PaulSchulz/paeiot-sensor-one/fritzing/board-v1_0.png

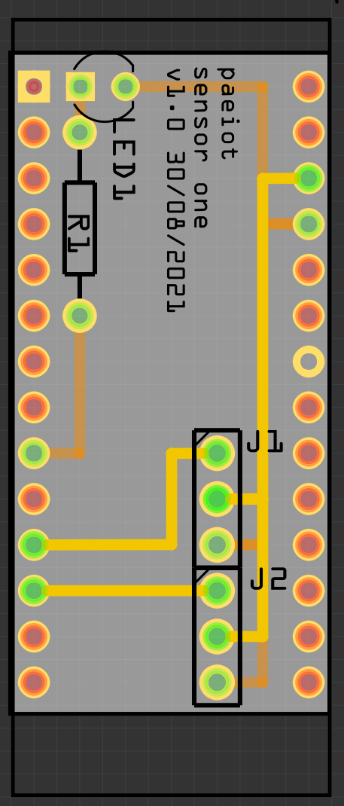
fritzing/board-v1_0.png
