PaulSchulz/paeiot-sensor-one/images/20210803_163039.jpg

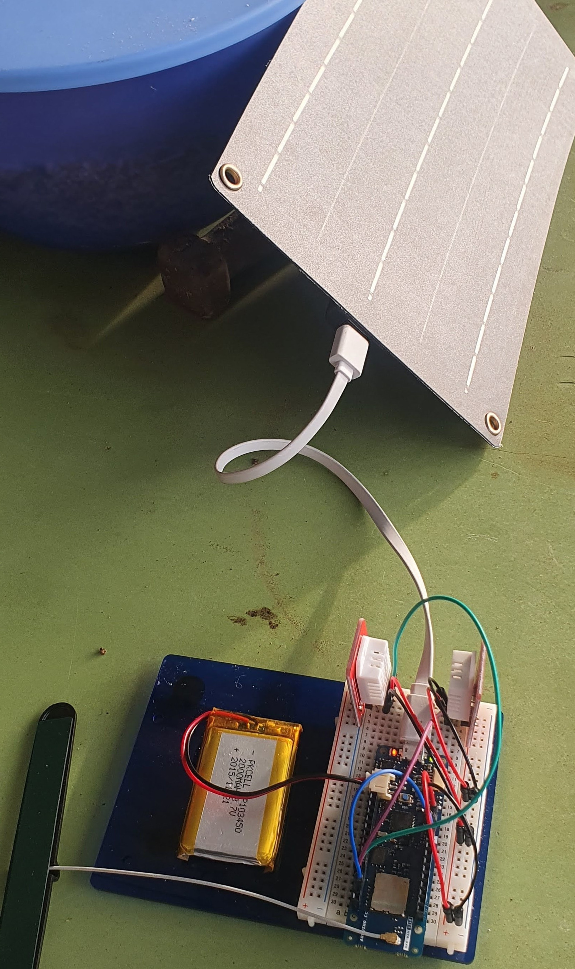
images/20210803_163039.jpg
