PaulSchulz/paeiot-sensor-one/images/20210814_2000_01.jpg

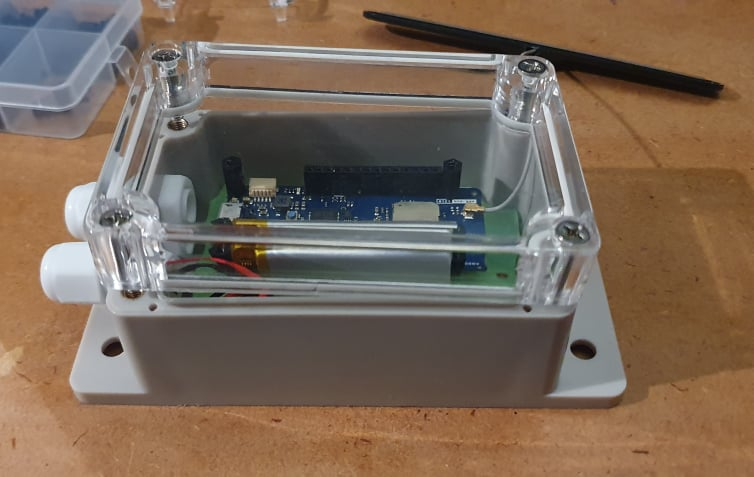
images/20210814_2000_01.jpg
