PaulSchulz/paeiot-sensor-one/images/20210823_110651_resized.jpg

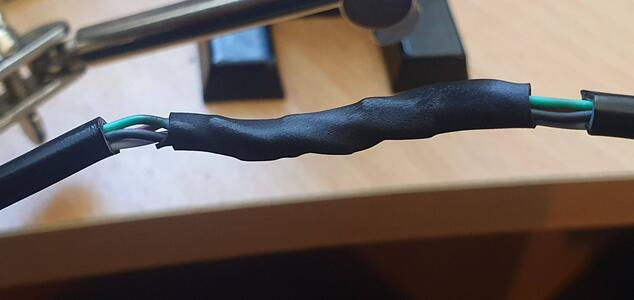
images/20210823_110651_resized.jpg
