PaulSchulz/paeiot-sensor-one/images/20210828_195500.jpg

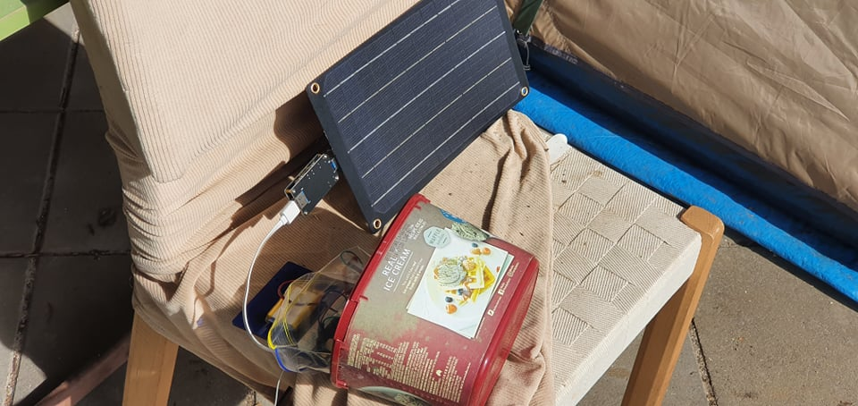
images/20210828_195500.jpg
