PaulSchulz/paeiot-sensor-one/images/20211008_182954.jpg

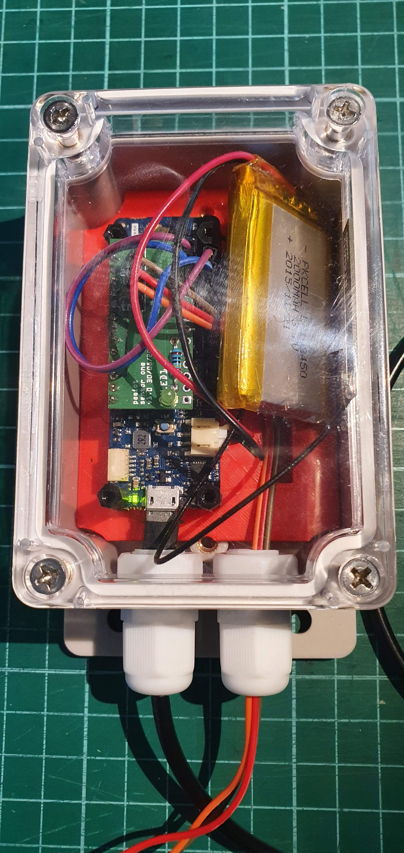
images/20211008_182954.jpg
