PaulSchulz/paeiot-sensor-one/images/20211029-093234.jpg

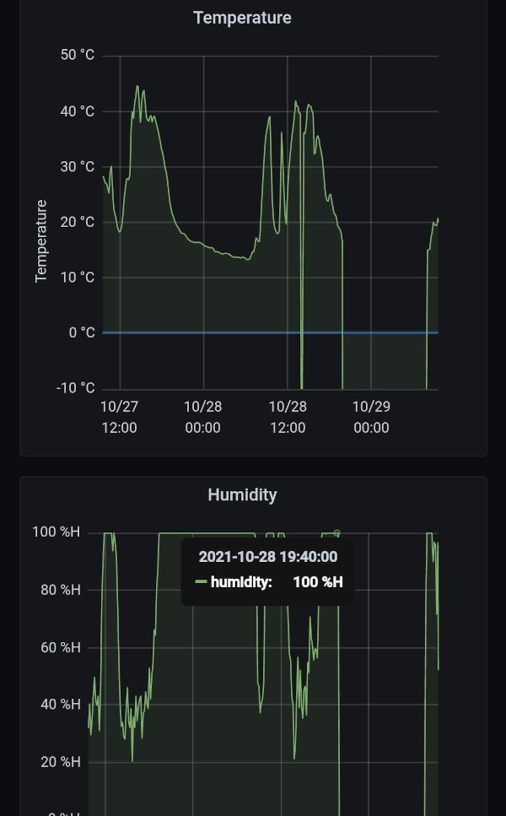
images/20211029-093234.jpg
