PaulSchulz/paeiot-sensor-one/images/228427619_3322535084639710_1404951063178568112_n.jpg

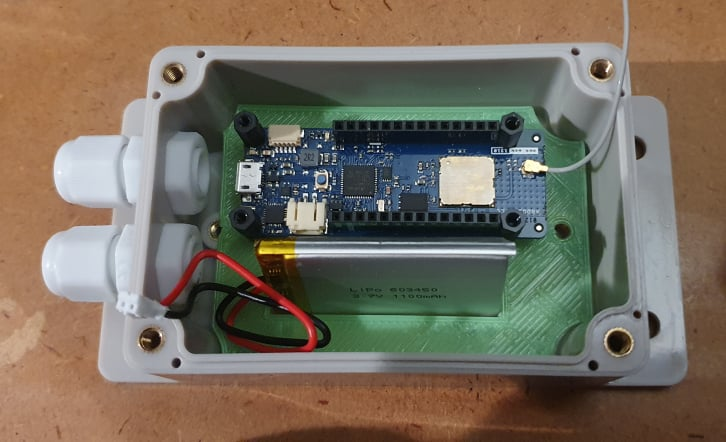
images/228427619_3322535084639710_1404951063178568112_n.jpg
