PaulSchulz/paeiot-sensor-one/images/230631305_171352048309334_1570531494024995739_n.jpg

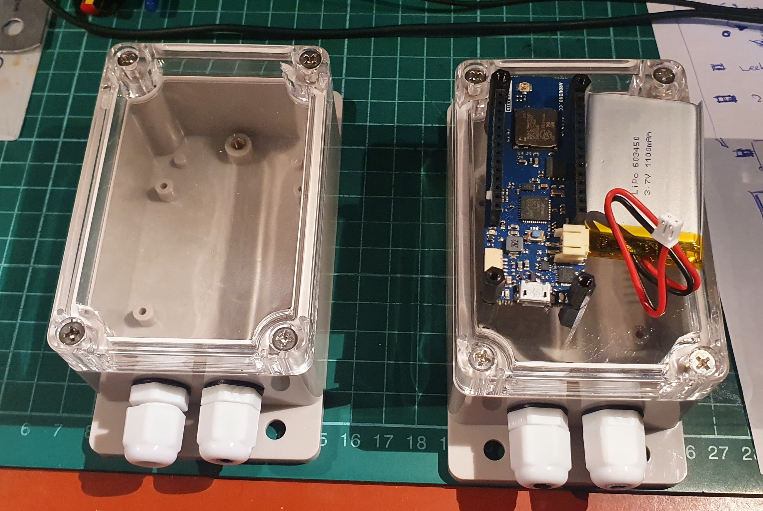
images/230631305_171352048309334_1570531494024995739_n.jpg
