PaulSchulz/paeiot-sensor-one/images/232836324_121206800151648_2778572270893868000_n.jpg

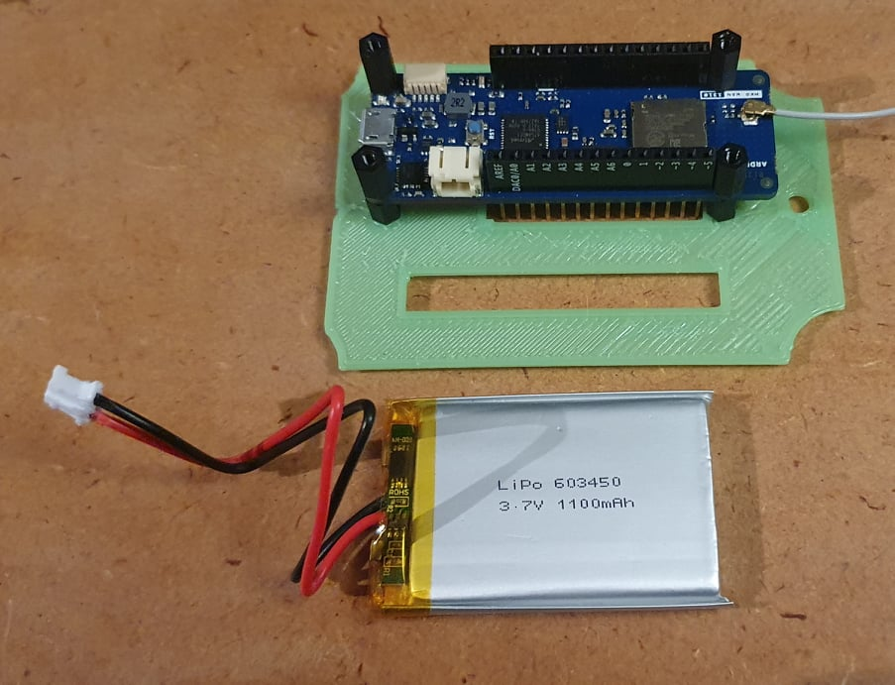
images/232836324_121206800151648_2778572270893868000_n.jpg
