PaulSchulz/paeiot-sensor-one/images/234786361_391616262325914_8475649943830079304_n.jpg

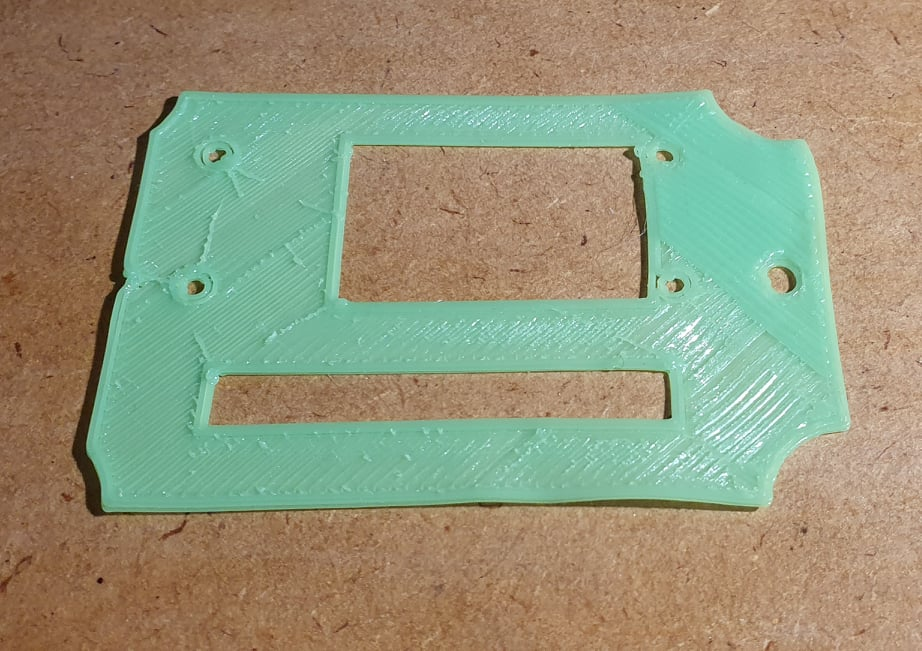
images/234786361_391616262325914_8475649943830079304_n.jpg
