PaulSchulz/paeiot-sensor-one/images/235867642_2991339191183786_8881488392173606955_n.jpg

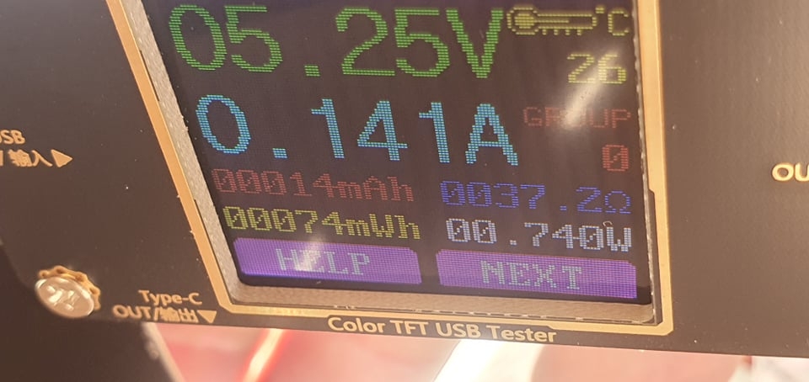
images/235867642_2991339191183786_8881488392173606955_n.jpg
