PaulSchulz/paeiot-sensor-one/images/MKRWAN1310-01.jpg

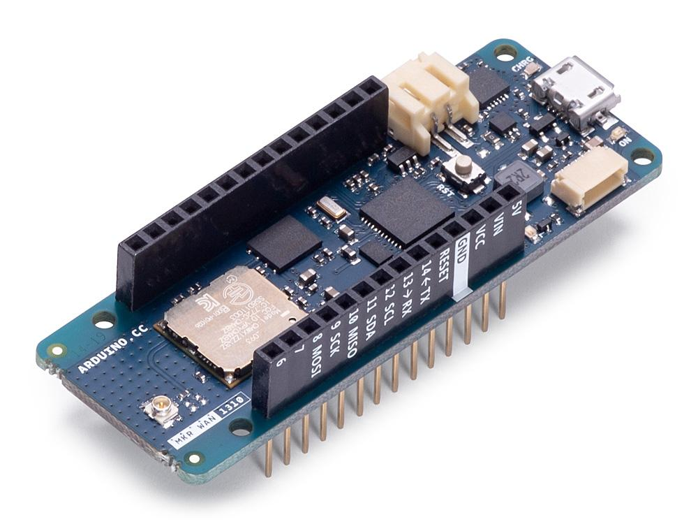
images/MKRWAN1310-01.jpg
