PaulSchulz/paeiot-sensor-one/images/MKRWAN1310-02.jpg

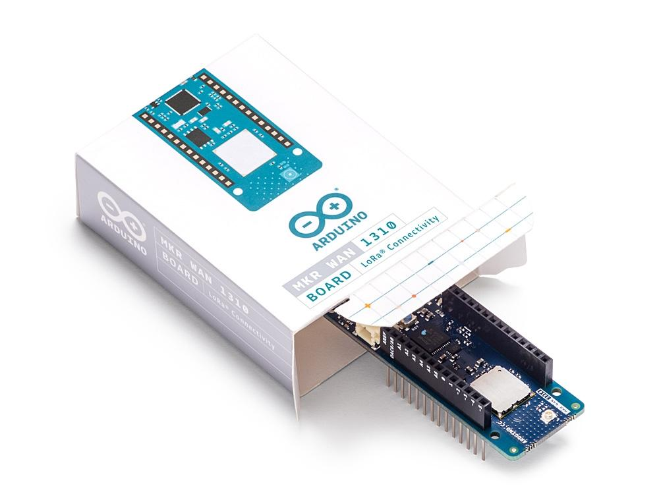
images/MKRWAN1310-02.jpg
