PaulSchulz/paeiot-sensor-one/images/MKRWAN1310-04.jpg

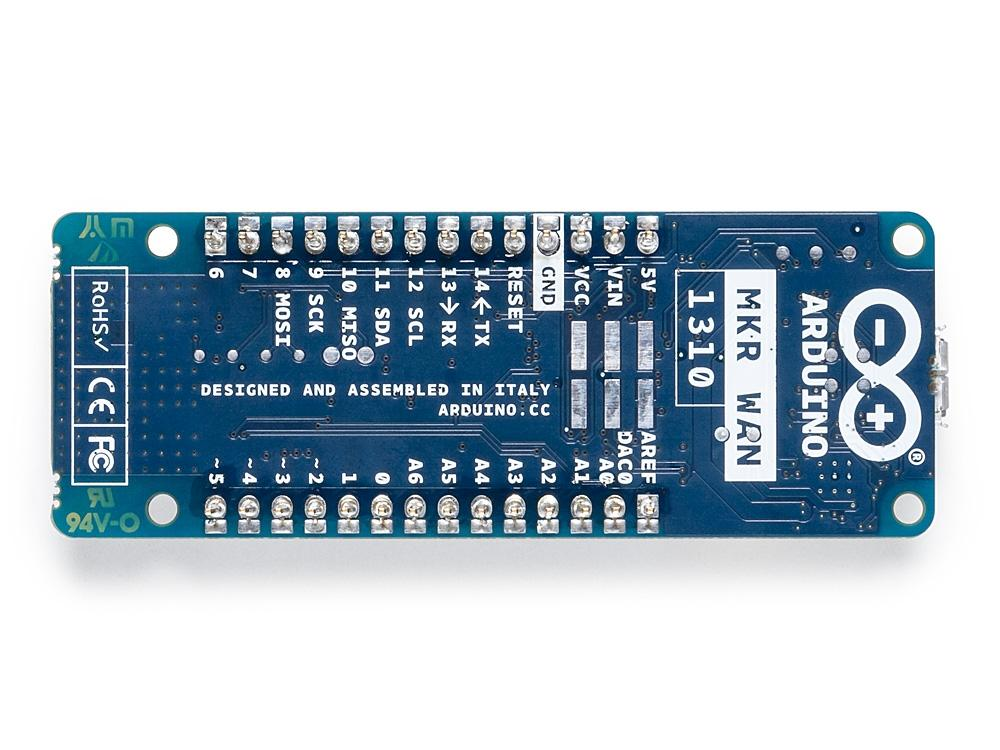
images/MKRWAN1310-04.jpg
