PaulSchulz/paeiot-sensor-one/images/MKRWAN1310-05.jpg

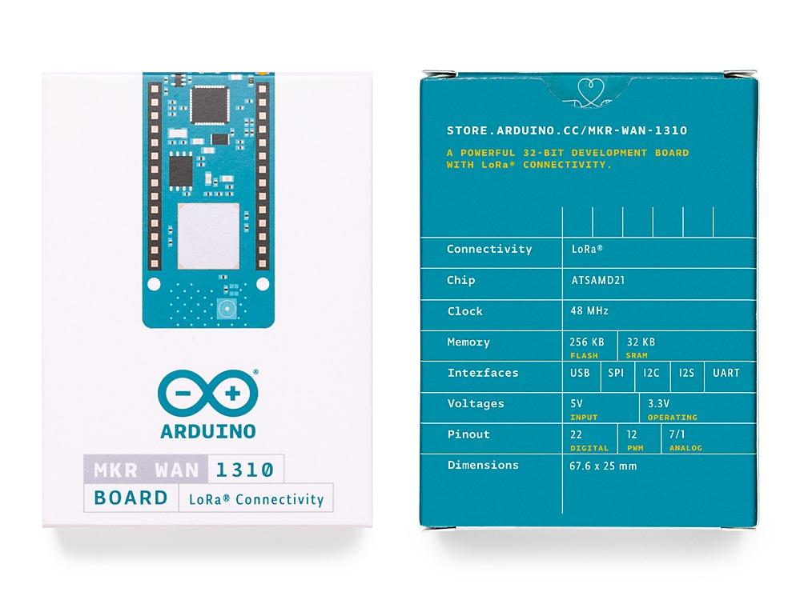
images/MKRWAN1310-05.jpg
