PaulSchulz/paeiot-sensor-one/images/MKRWAN1310-06.jpg

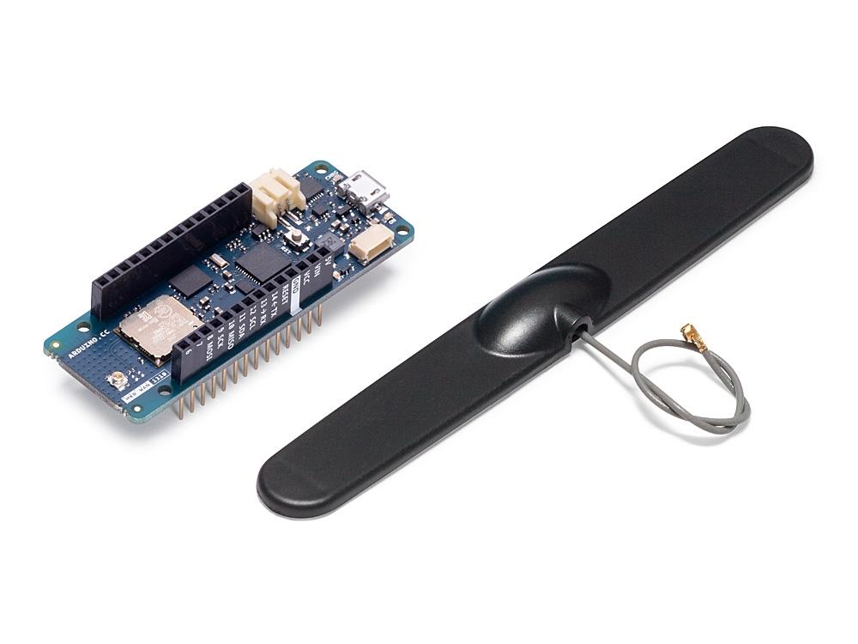
images/MKRWAN1310-06.jpg
